Rudraa-25/Macropad/media/IMG_20260529_175152454.jpg

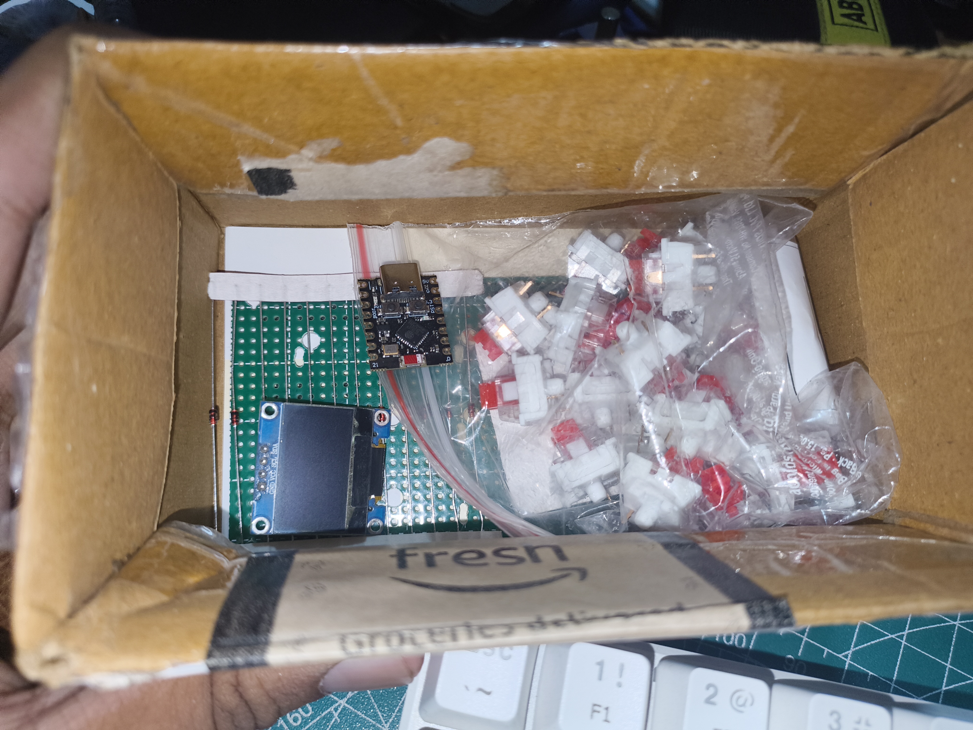
media/IMG_20260529_175152454.jpg
