Rudraa-25/Macropad/media/IMG_20260602_213806897.jpg

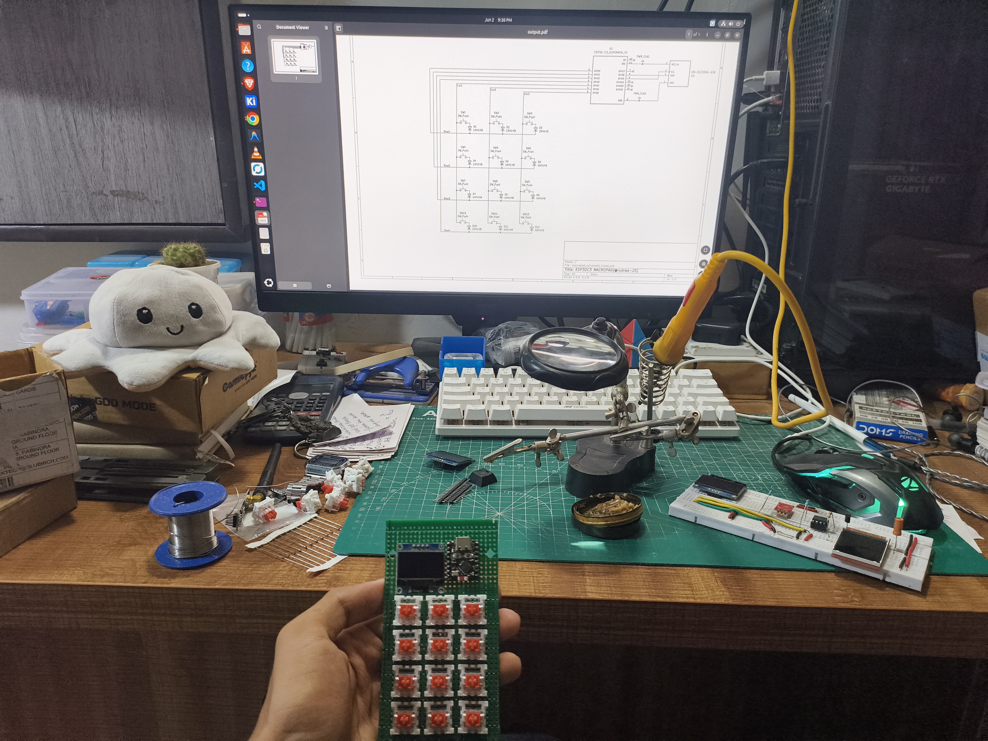
media/IMG_20260602_213806897.jpg
