Rudraa-25/Macropad/media/IMG_20260603_223023844.jpg

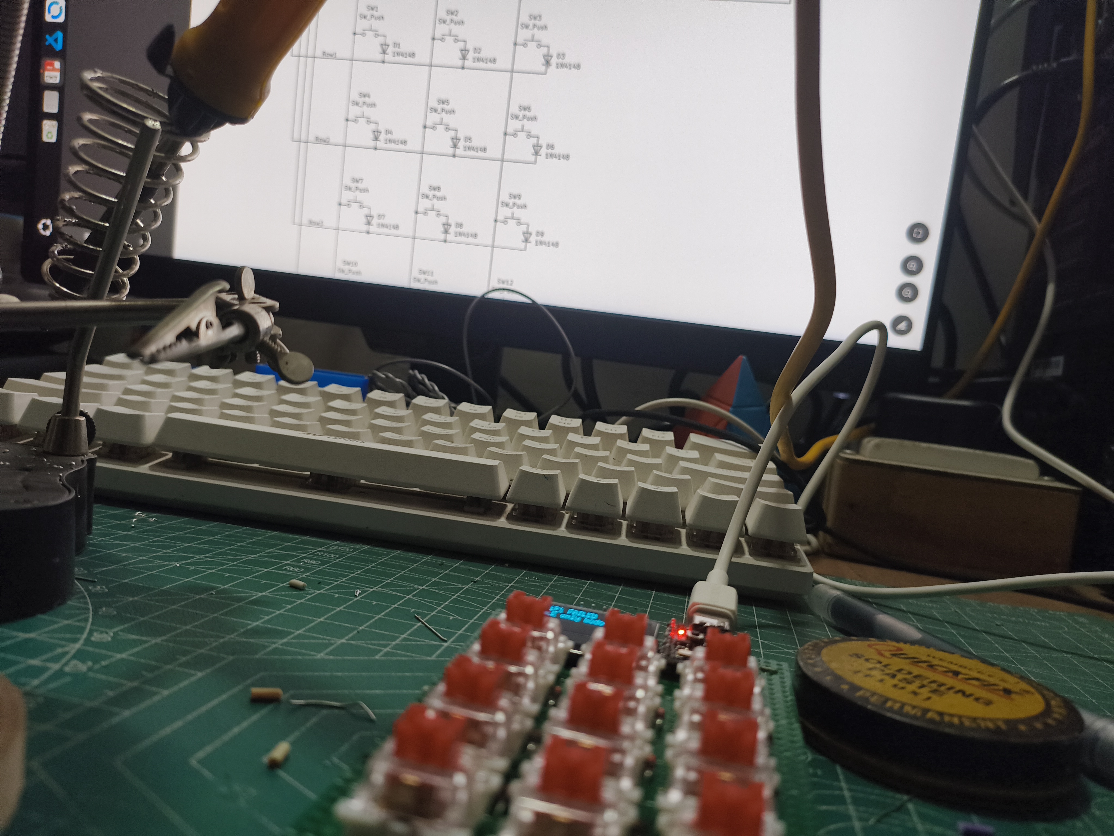
media/IMG_20260603_223023844.jpg
