Rudraa-25/Macropad/media/WhatsApp Image 2026-06-05 at 6.21.26 PM (2).jpeg

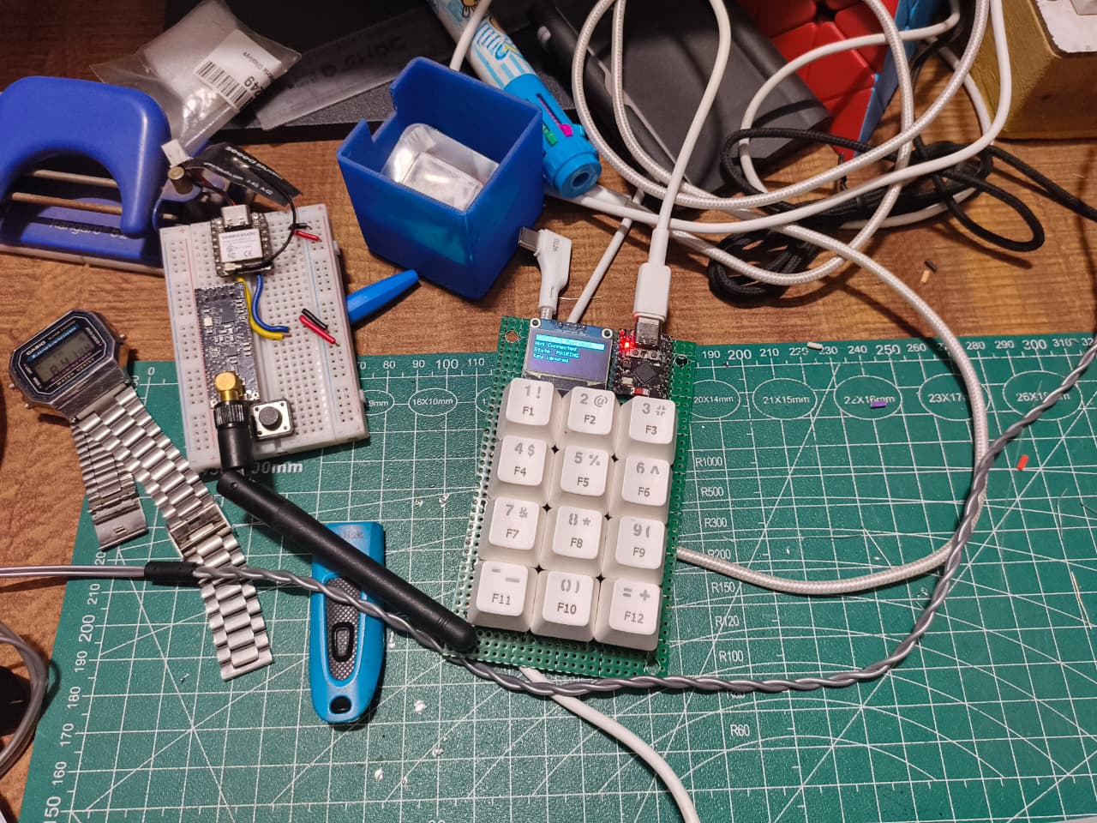
media/WhatsApp Image 2026-06-05 at 6.21.26 PM (2).jpeg
